GigaOhms/SENTSOR-ESP32WR32UE/.github/{1876FB12-8DDD-41EA-97F9-A7A06D77545C}.png

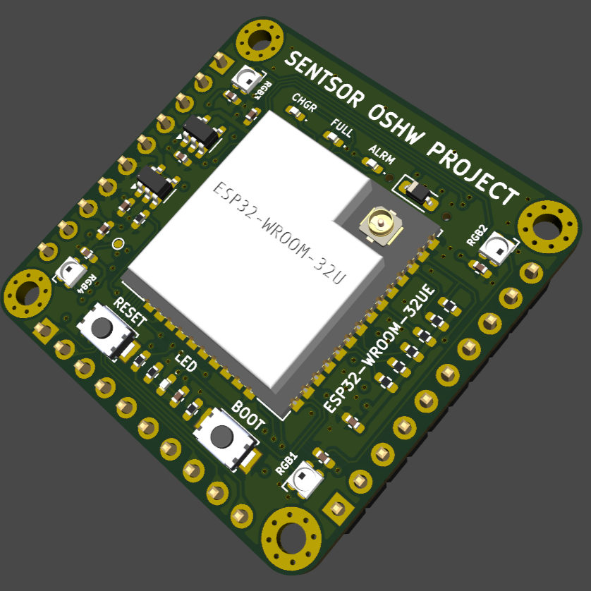
.github/{1876FB12-8DDD-41EA-97F9-A7A06D77545C}.png
